Tr3v0r86/turnkeep/media/exploded.png

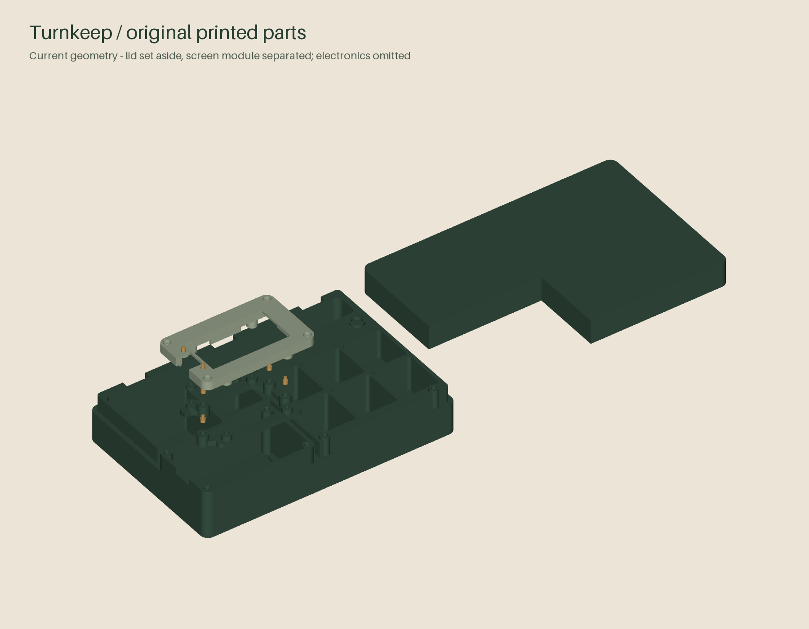
media/exploded.png
