Tr3v0r86/turnkeep/media/hero.png

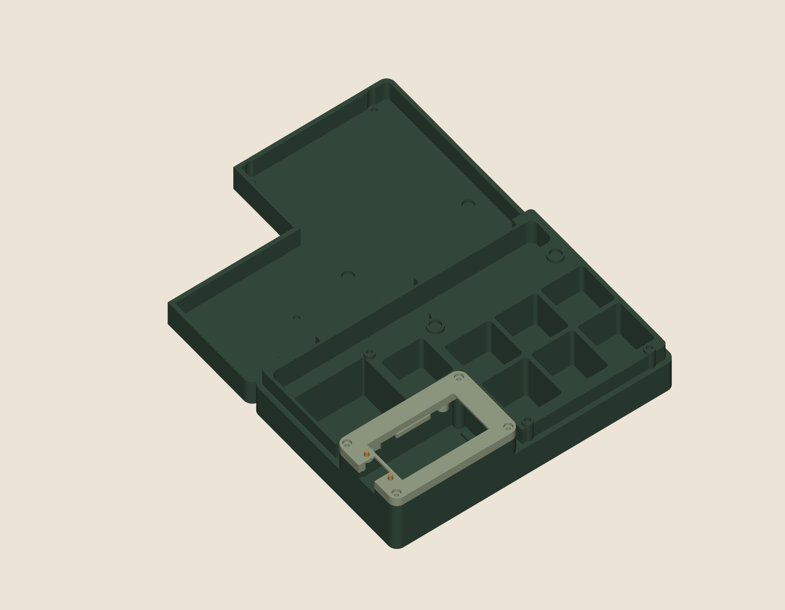
media/hero.png
