Tr3v0r86/turnkeep/media/kit-layout.png

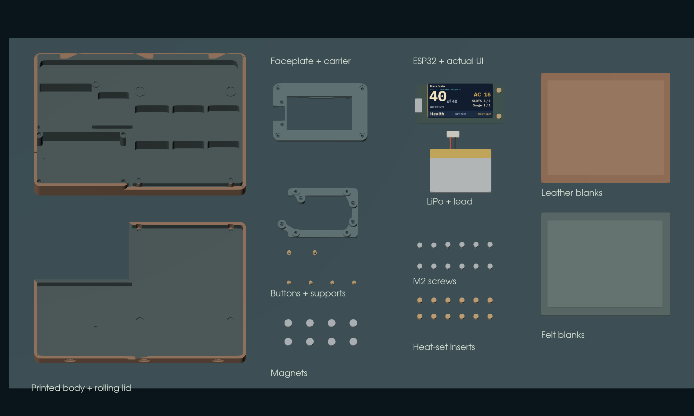
media/kit-layout.png
