Tr3v0r86/turnkeep/media/module.png

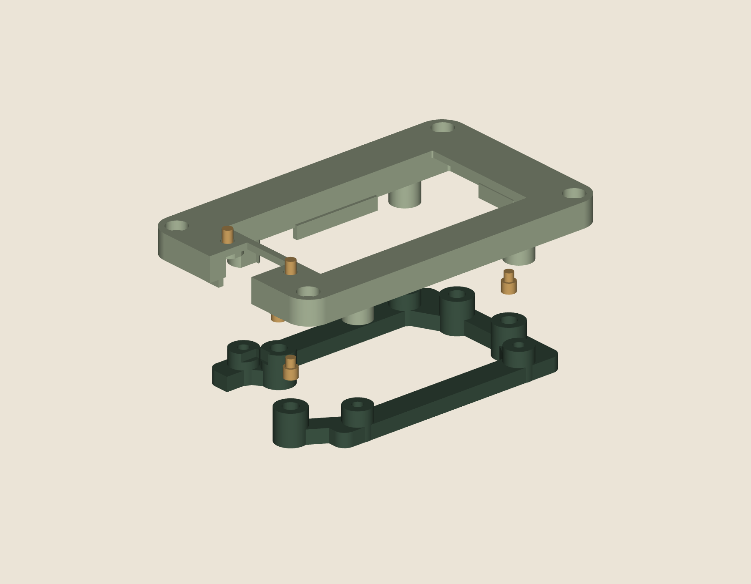
media/module.png
