Tr3v0r86/turnkeep/media/product-closed.png

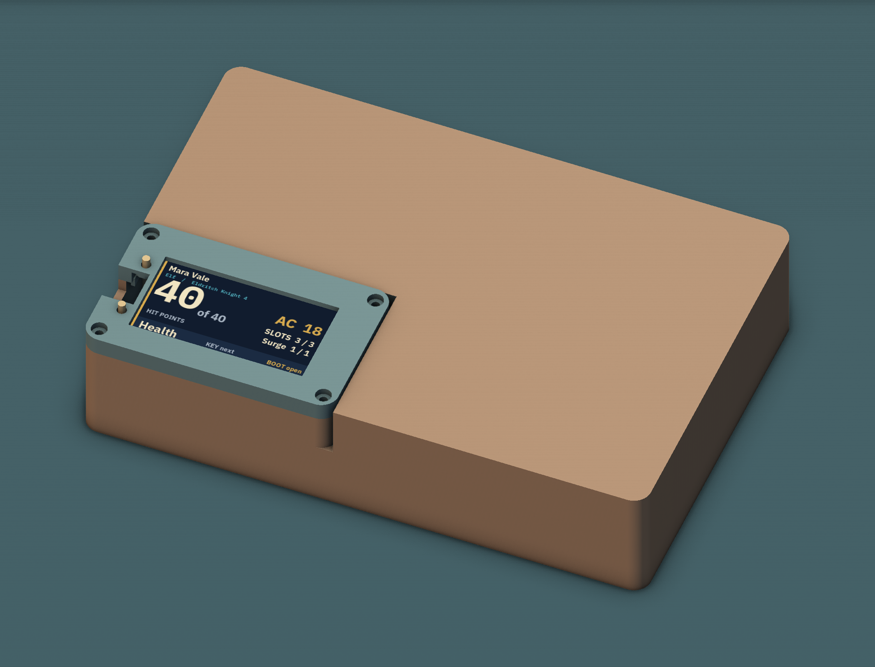
media/product-closed.png
