Tr3v0r86/turnkeep/media/product-hero.png

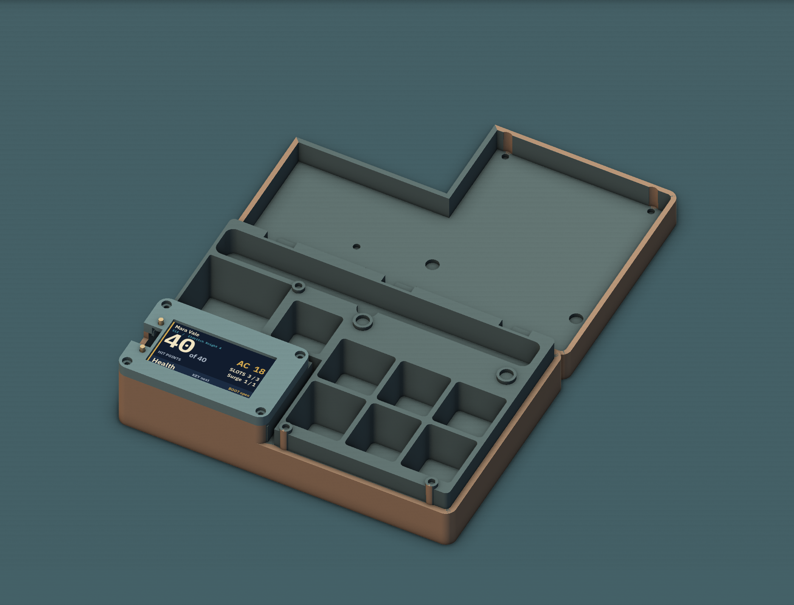
media/product-hero.png
