Tr3v0r86/turnkeep/site/assets/screen.png

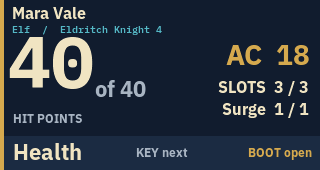
site/assets/screen.png
