Tr3v0r86/turnkeep/hardware/preview_meshes/pad_3.stl

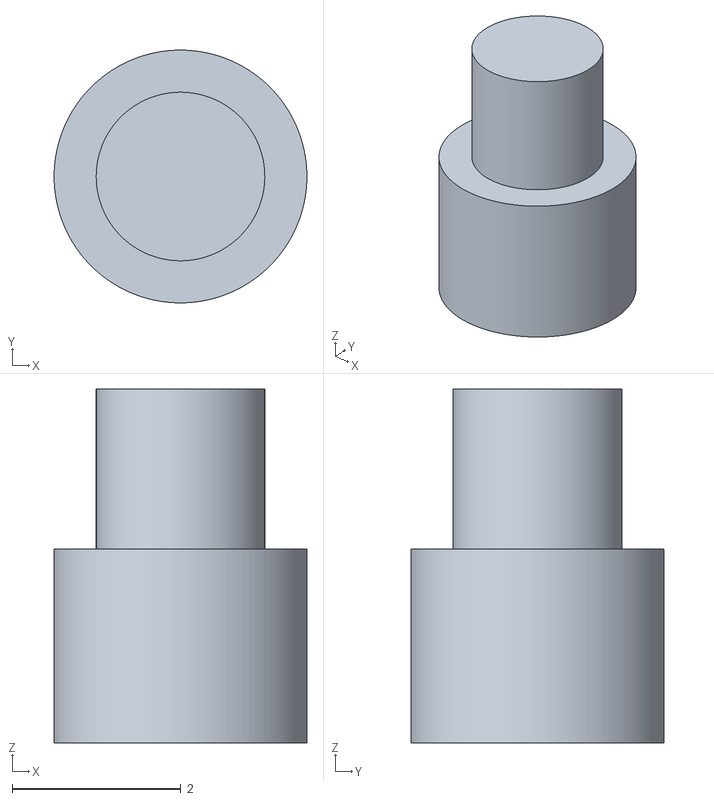
[picture p29: CAD file, 2026-09-19]
hardware/preview_meshes/pad_3.stl
3.00 x 3.00 x 4.20
