Tr3v0r86/turnkeep/hardware/concepts/round/body.stl

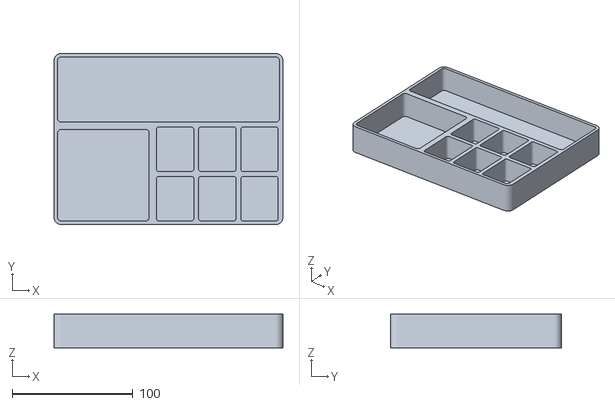
[picture p30: CAD file, 2026-09-19]
hardware/concepts/round/body.stl
190.0 x 142.0 x 28.0
