Tr3v0r86/turnkeep/hardware/preview_meshes/deck.stl

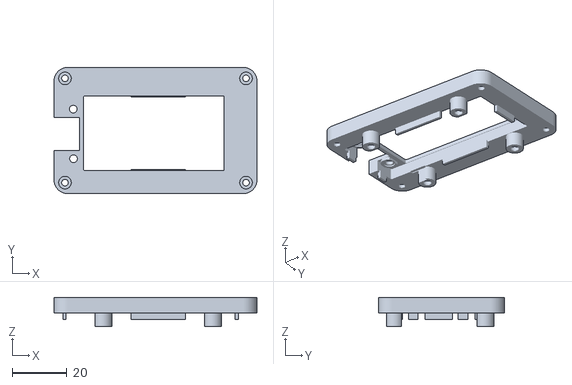
[picture p31: CAD file, 2026-09-19]
hardware/preview_meshes/deck.stl
74.0 x 46.0 x 10.6
