Tr3v0r86/turnkeep/hardware/concepts/cyd/concept.step

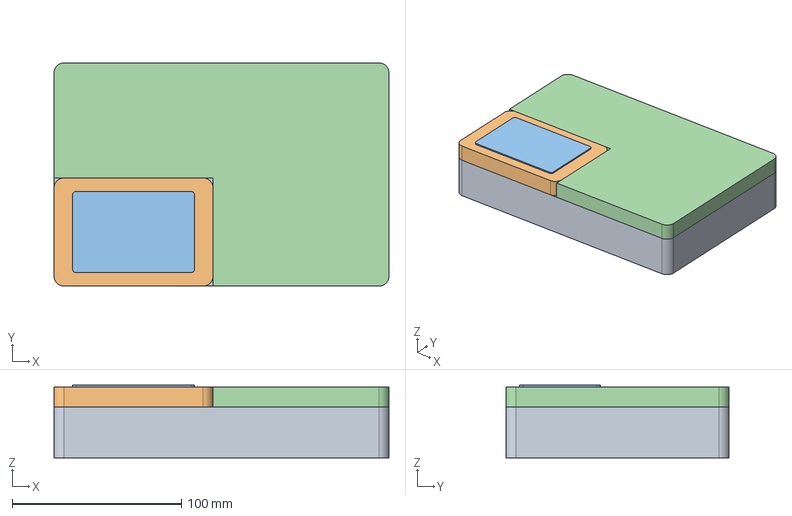
[picture p32: CAD file, 2026-09-19]
hardware/concepts/cyd/concept.step
198.0 x 132.0 x 43.0 mm
deck
screen_placeholder
lid
