Tr3v0r86/turnkeep/hardware/concepts/epaper/concept.step

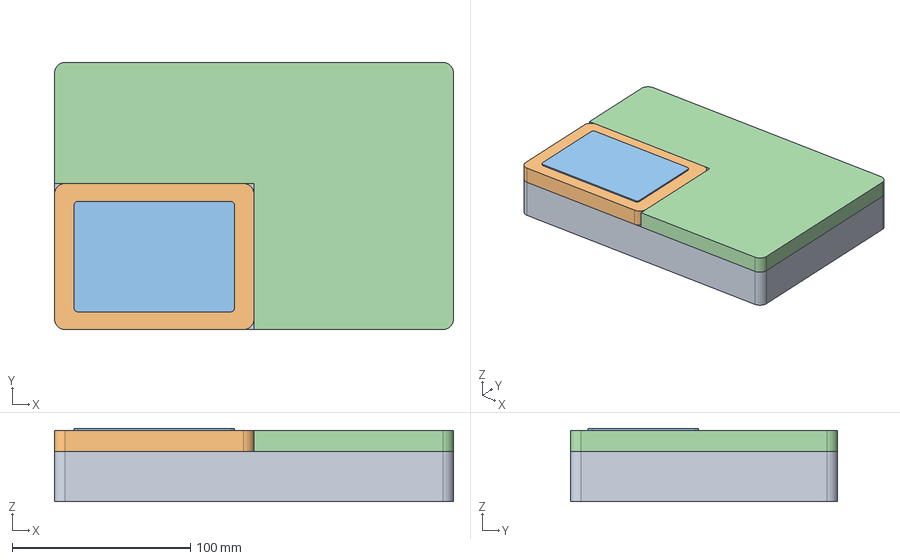
[picture p33: CAD file, 2026-09-19]
hardware/concepts/epaper/concept.step
224.0 x 150.0 x 41.0 mm
deck
screen_placeholder
lid
