Tr3v0r86/turnkeep/hardware/concepts/round/screen_placeholder.stl

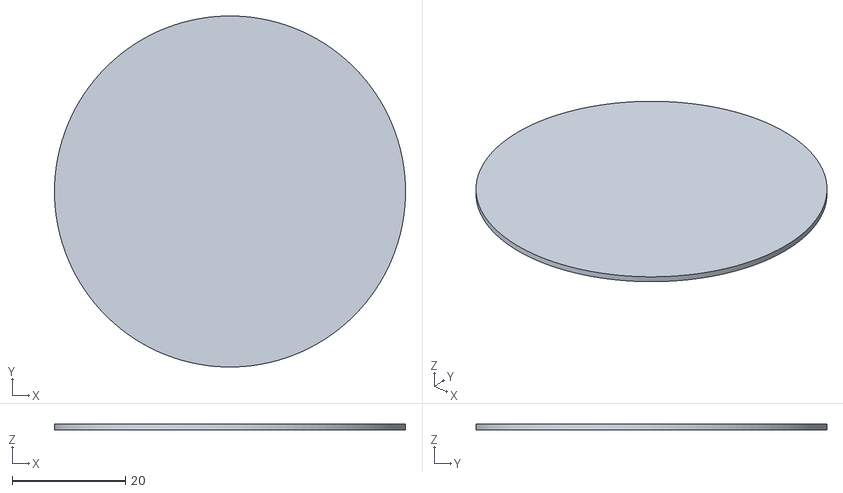
[picture p34: CAD file, 2026-09-19]
hardware/concepts/round/screen_placeholder.stl
62.0 x 62.0 x 1.00
