Tr3v0r86/turnkeep/hardware/concepts/cyd/screen_placeholder.stl

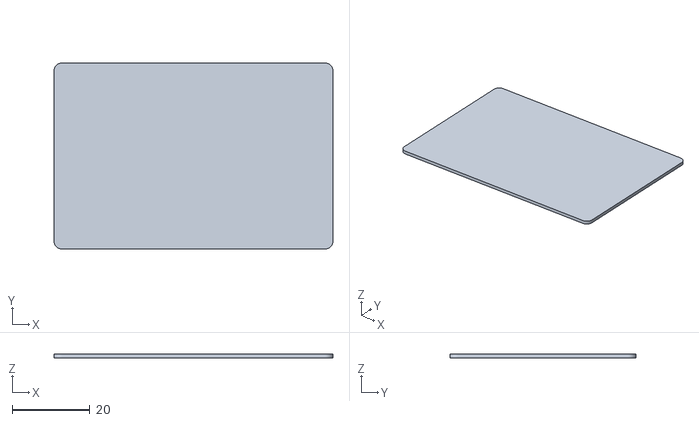
[picture p35: CAD file, 2026-09-19]
hardware/concepts/cyd/screen_placeholder.stl
72.0 x 48.0 x 1.00
