Tr3v0r86/turnkeep/hardware/concepts/epaper/deck.stl

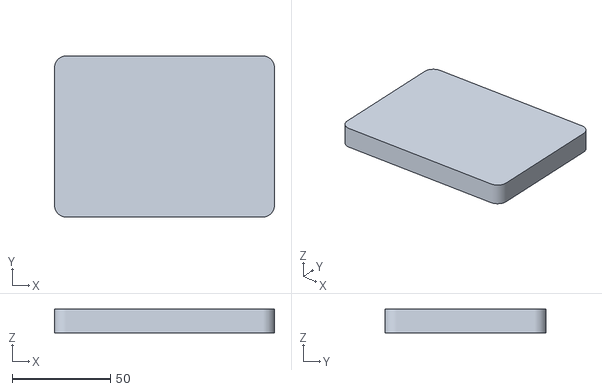
[picture p36: CAD file, 2026-09-19]
hardware/concepts/epaper/deck.stl
112.0 x 82.0 x 12.0
