Tr3v0r86/turnkeep/hardware/concepts/round/deck.stl

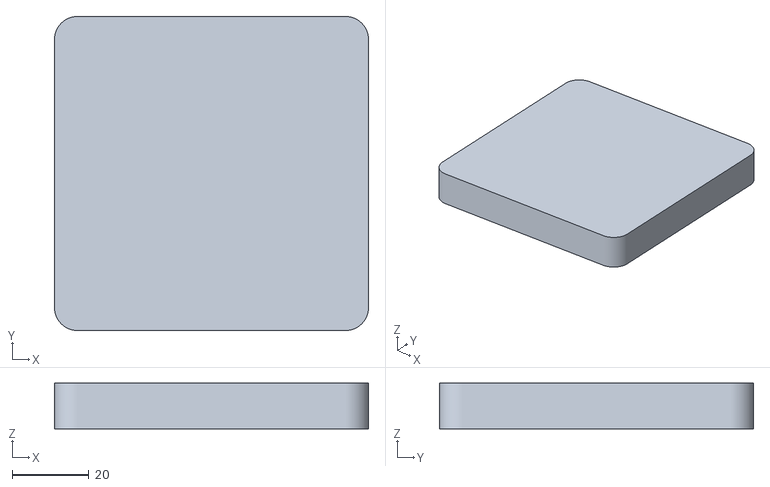
[picture p37: CAD file, 2026-09-19]
hardware/concepts/round/deck.stl
82.0 x 82.0 x 12.0
