Tr3v0r86/turnkeep/hardware/preview_meshes/button_1.stl

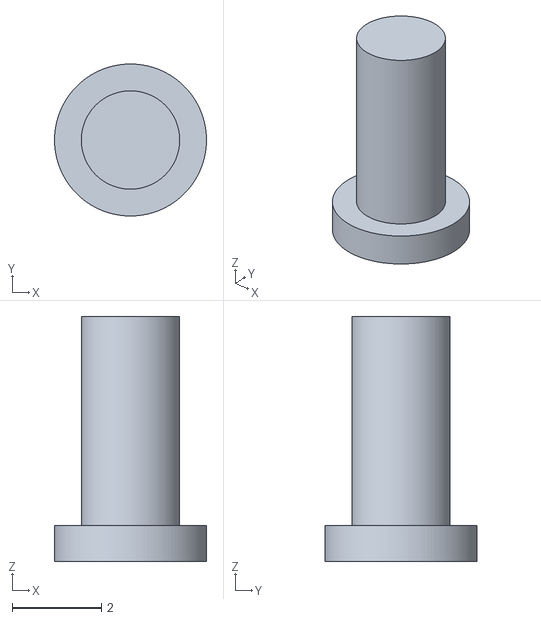
[picture p38: CAD file, 2026-09-19]
hardware/preview_meshes/button_1.stl
3.40 x 3.40 x 5.48
