Tr3v0r86/turnkeep/hardware/stl/10_lid_fit_female.stl

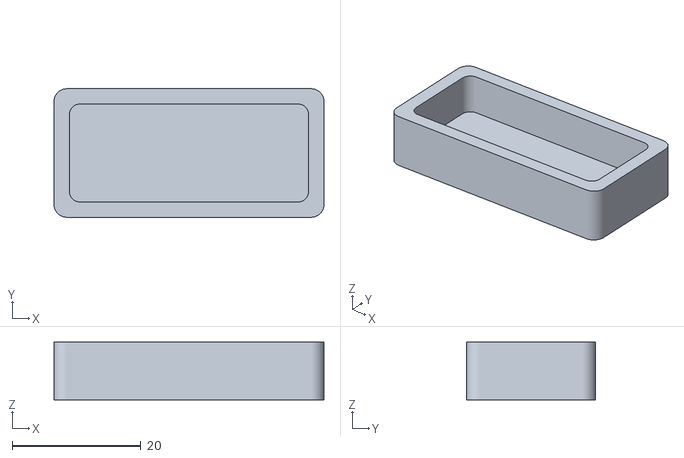
[picture p39: CAD file, 2026-09-19]
hardware/stl/10_lid_fit_female.stl
42.0 x 20.0 x 9.00
