Tr3v0r86/turnkeep/hardware/stl/11_dock_socket_coupon.stl

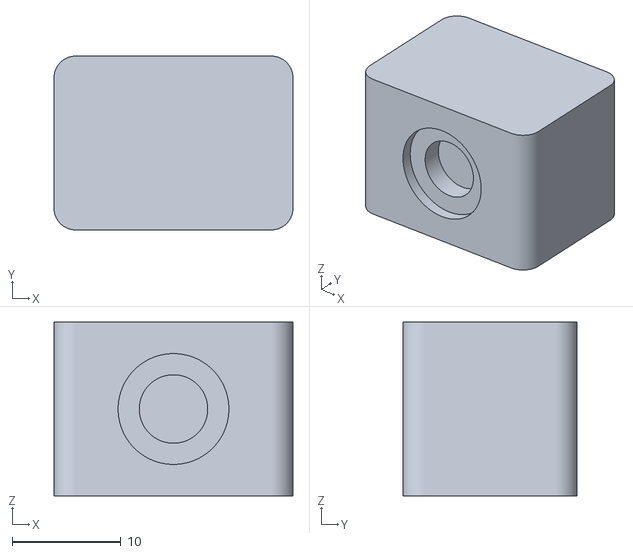
[picture p40: CAD file, 2026-09-19]
hardware/stl/11_dock_socket_coupon.stl
22.0 x 16.0 x 16.0
