Tr3v0r86/turnkeep/hardware/stl/04_adjustable_retainer_v03.stl

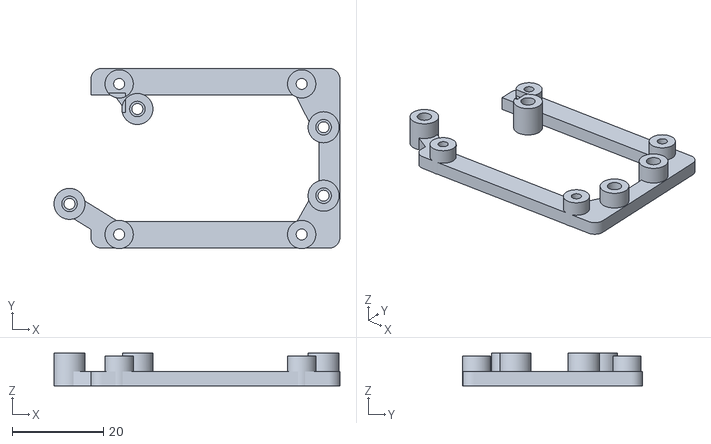
[picture p41: CAD file, 2026-09-19]
hardware/stl/04_adjustable_retainer_v03.stl
62.7 x 39.5 x 7.20
