Tr3v0r86/turnkeep/hardware/stl/12_dock_collar_coupon.stl

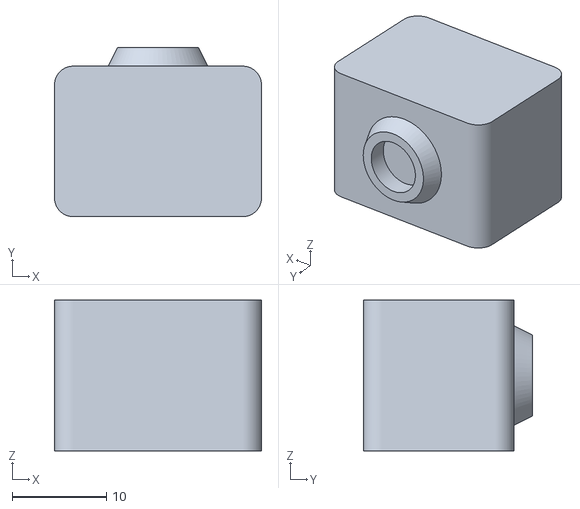
[picture p42: CAD file, 2026-09-19]
hardware/stl/12_dock_collar_coupon.stl
22.0 x 18.0 x 16.0
