Tr3v0r86/turnkeep/hardware/stl/09_lid_fit_male.stl

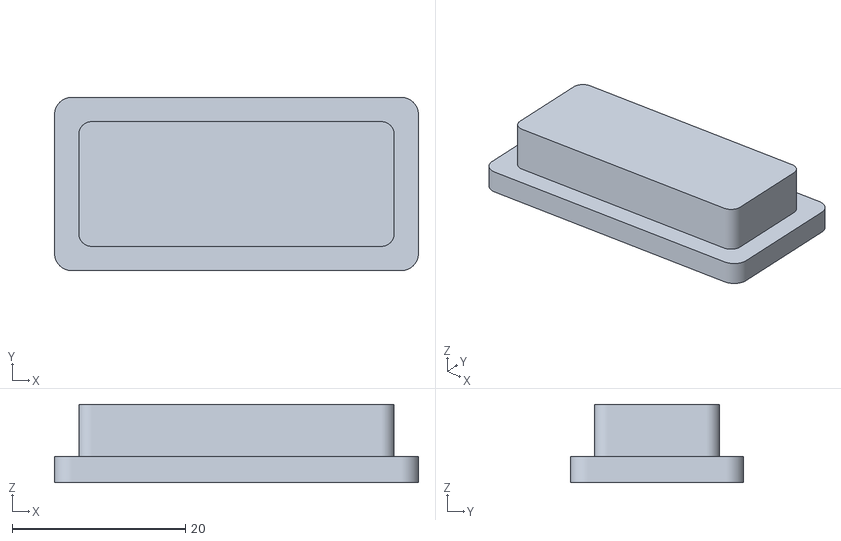
[picture p43: CAD file, 2026-09-19]
hardware/stl/09_lid_fit_male.stl
42.0 x 20.0 x 9.00
